CampelloManuel/progetto-esame/datasheets/sonda-ntc_sih010.bmp

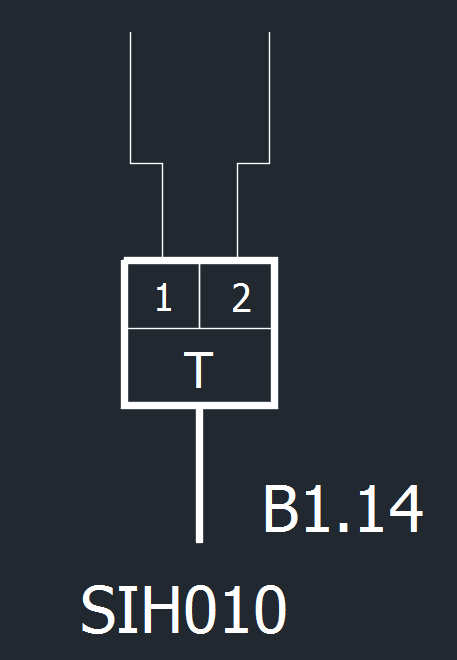
datasheets/sonda-ntc_sih010.bmp
