CampelloManuel/progetto-esame/esempi_arduino/prove_accessori/display_collegamento 2.jpg

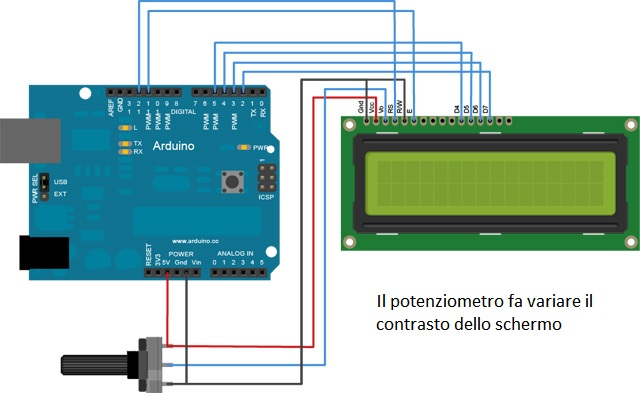
esempi_arduino/prove_accessori/display_collegamento 2.jpg
