CampelloManuel/progetto-esame/immagini_cogeneratore/IMG-20161022-WA0023.jpg

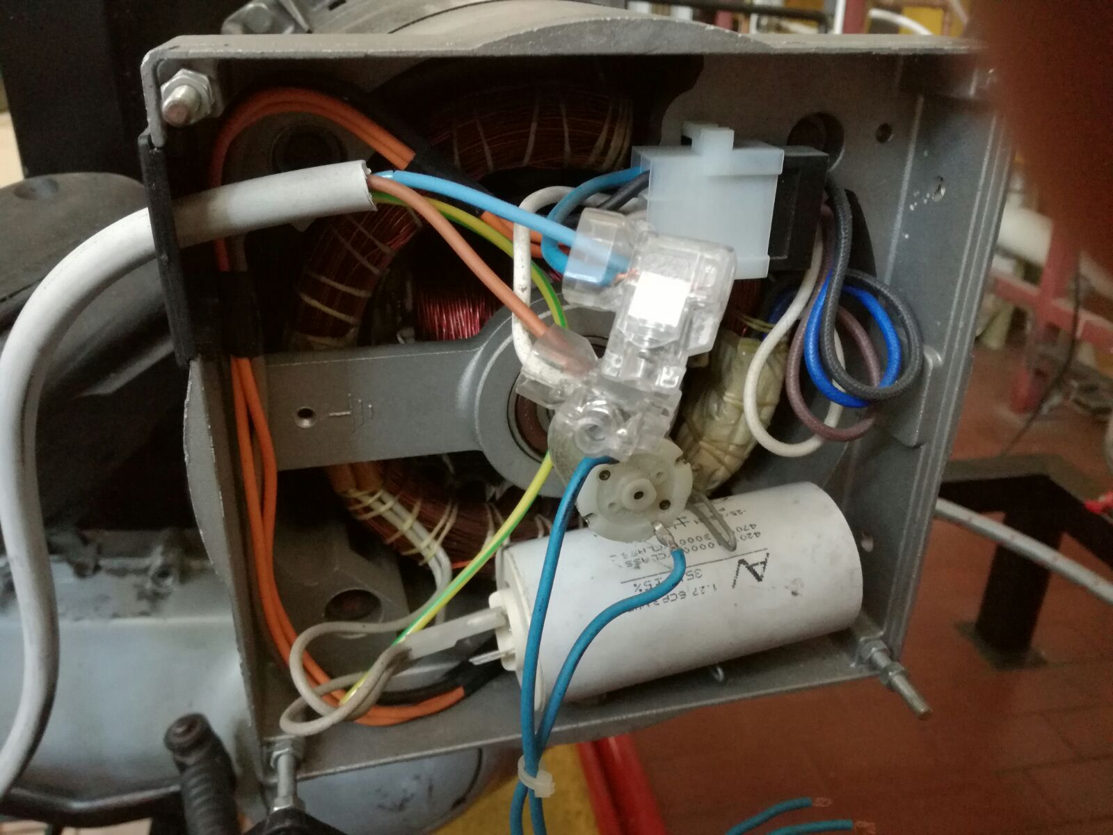
immagini_cogeneratore/IMG-20161022-WA0023.jpg
