CampelloManuel/progetto-esame/immagini_cogeneratore/IMG-20161022-WA0027.jpg

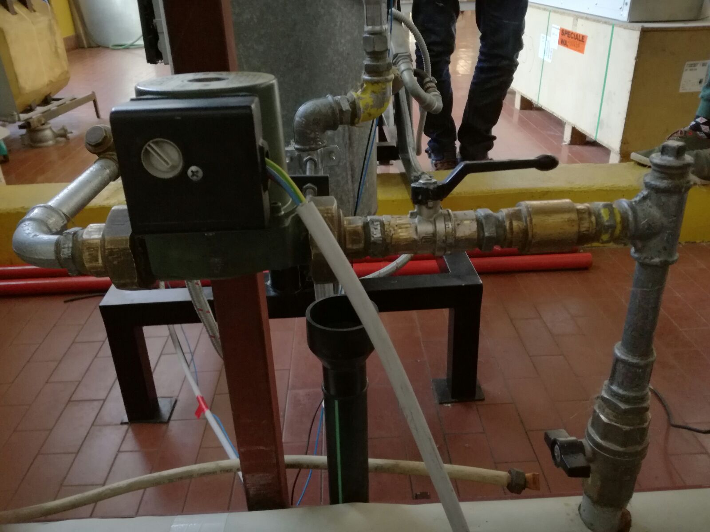
immagini_cogeneratore/IMG-20161022-WA0027.jpg
