CampelloManuel/progetto-esame/immagini_cogeneratore/IMG-20170110-WA0005.jpg

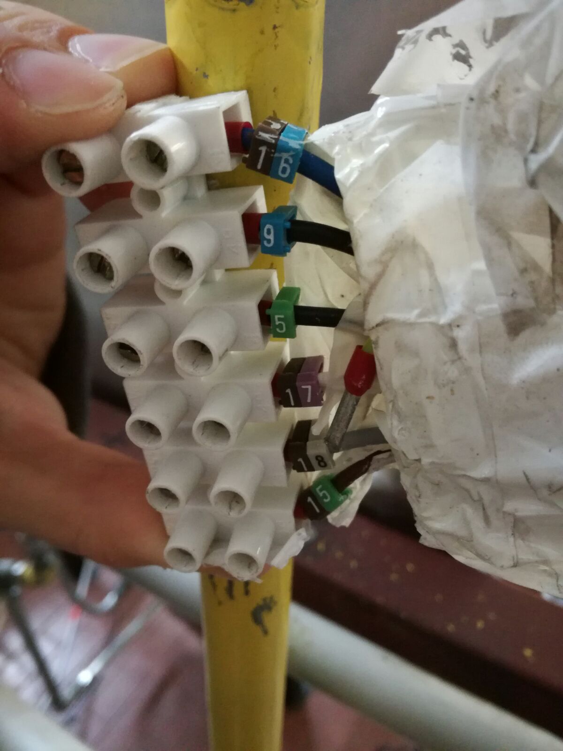
immagini_cogeneratore/IMG-20170110-WA0005.jpg
