CampelloManuel/progetto-esame/immagini_cogeneratore/IMG-20170610-WA0005.jpg

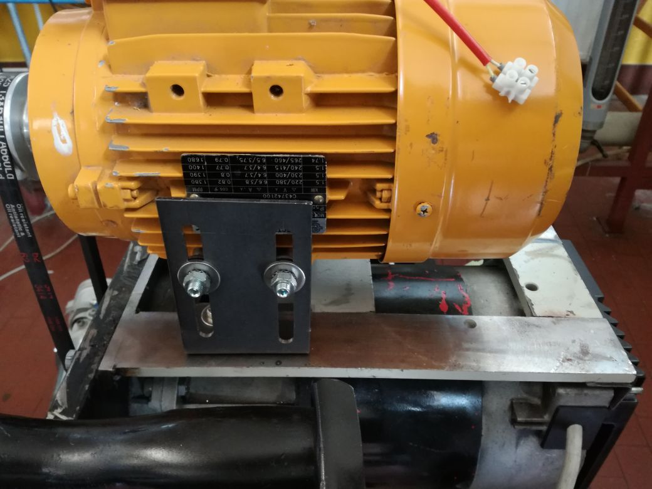
immagini_cogeneratore/IMG-20170610-WA0005.jpg
