CampelloManuel/progetto-esame/immagini_cogeneratore/IMG-20170610-WA0010.jpg

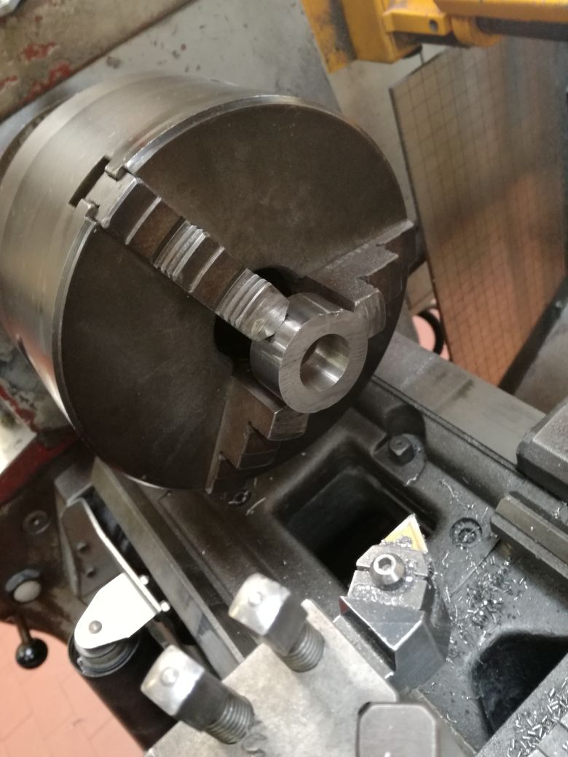
immagini_cogeneratore/IMG-20170610-WA0010.jpg
