CampelloManuel/progetto-esame/immagini_cogeneratore/IMG_20161109_105624.jpg

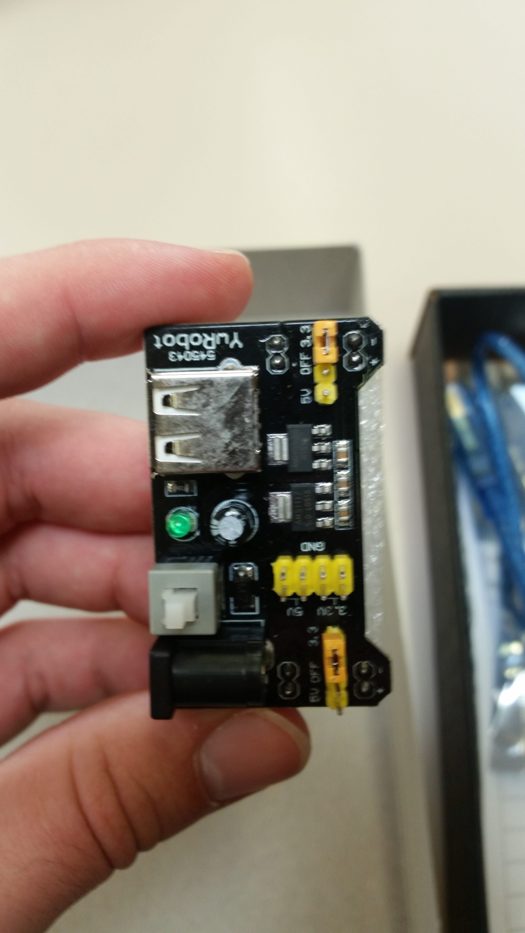
immagini_cogeneratore/IMG_20161109_105624.jpg
