CampelloManuel/progetto-esame/immagini_cogeneratore/IMG_20161201_091057.jpg

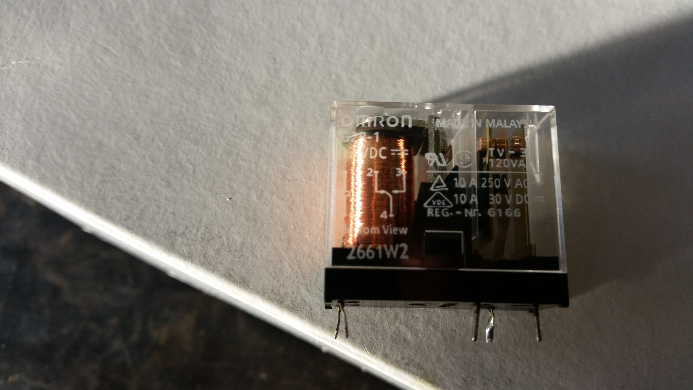
immagini_cogeneratore/IMG_20161201_091057.jpg
