CampelloManuel/progetto-esame/immagini_cogeneratore/IMG_20161201_091629.jpg

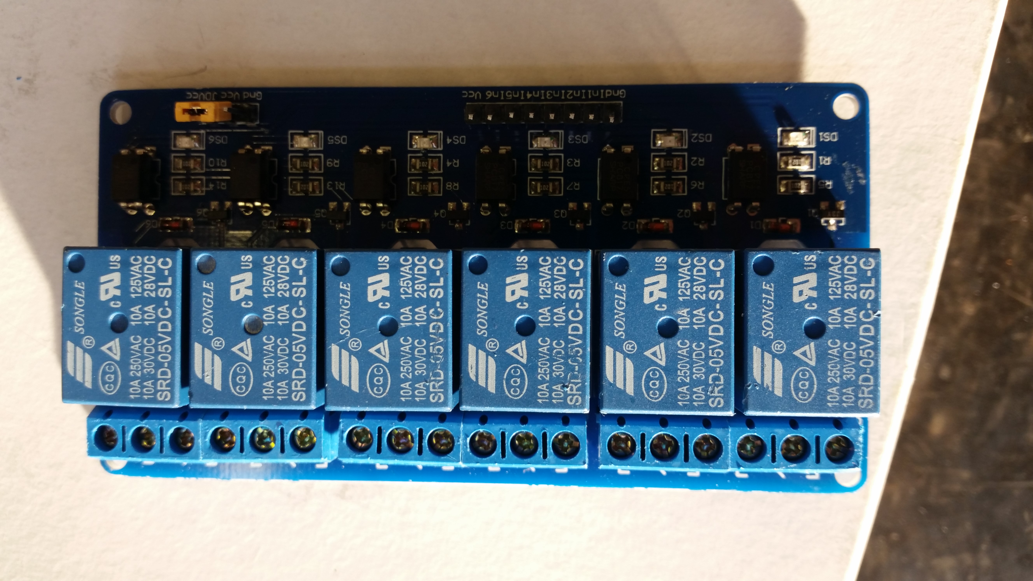
immagini_cogeneratore/IMG_20161201_091629.jpg
