CampelloManuel/progetto-esame/immagini_cogeneratore/IMG_20170113_105047.jpg

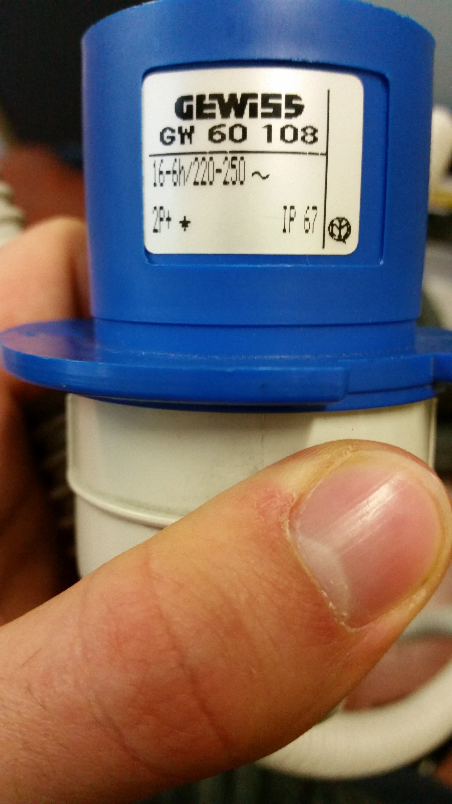
immagini_cogeneratore/IMG_20170113_105047.jpg
