CampelloManuel/progetto-esame/immagini_cogeneratore/IMG_20170113_111320.jpg

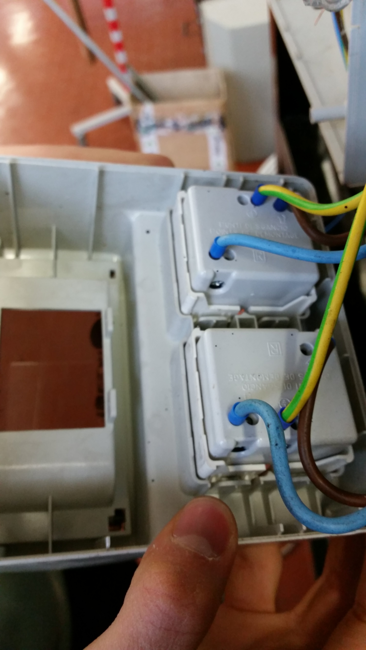
immagini_cogeneratore/IMG_20170113_111320.jpg
