CampelloManuel/progetto-esame/immagini_cogeneratore/IMG_20170120_110058.jpg

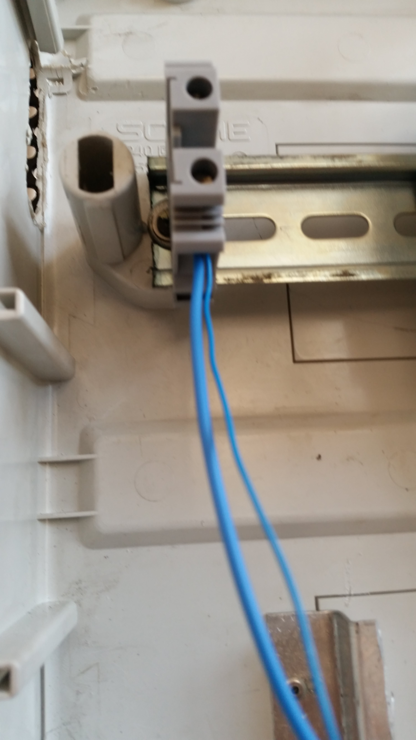
immagini_cogeneratore/IMG_20170120_110058.jpg
