CampelloManuel/progetto-esame/immagini_cogeneratore/IMG_20170120_111345.jpg

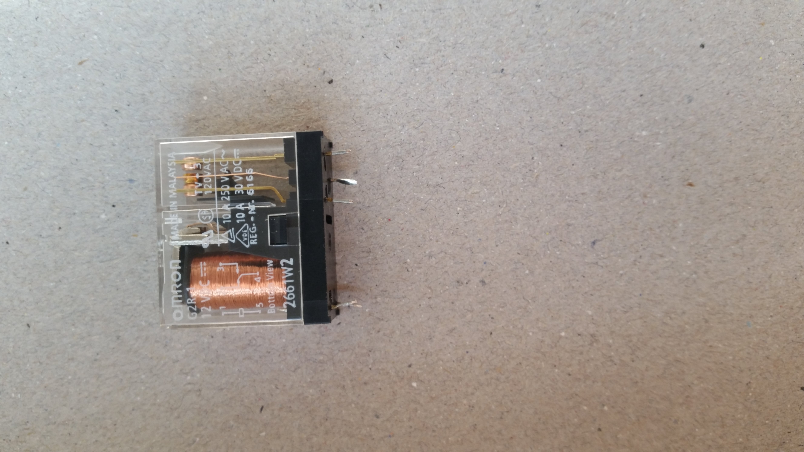
immagini_cogeneratore/IMG_20170120_111345.jpg
