CampelloManuel/progetto-esame/immagini_cogeneratore/IMG_20170317_114829.jpg

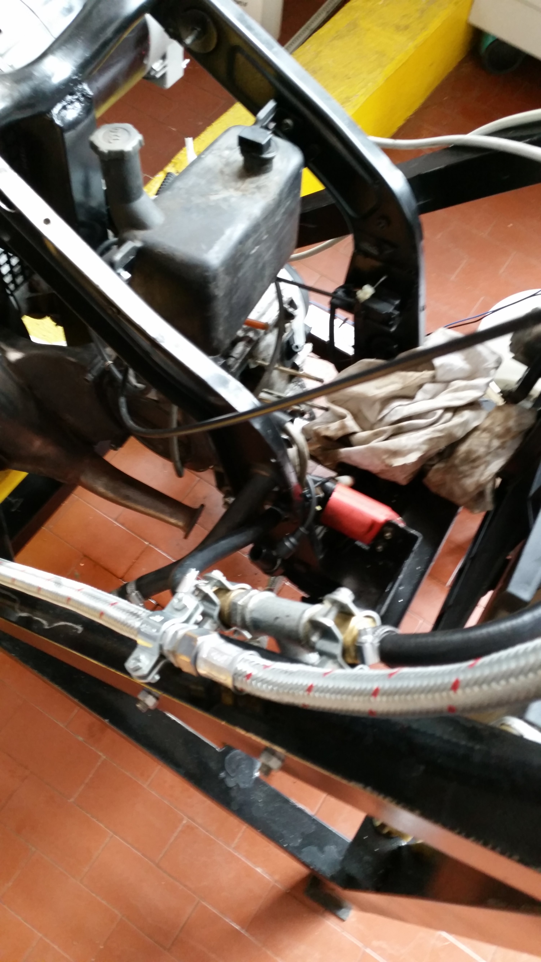
immagini_cogeneratore/IMG_20170317_114829.jpg
