CampelloManuel/progetto-esame/immagini_cogeneratore/IMG_20170317_114911.jpg

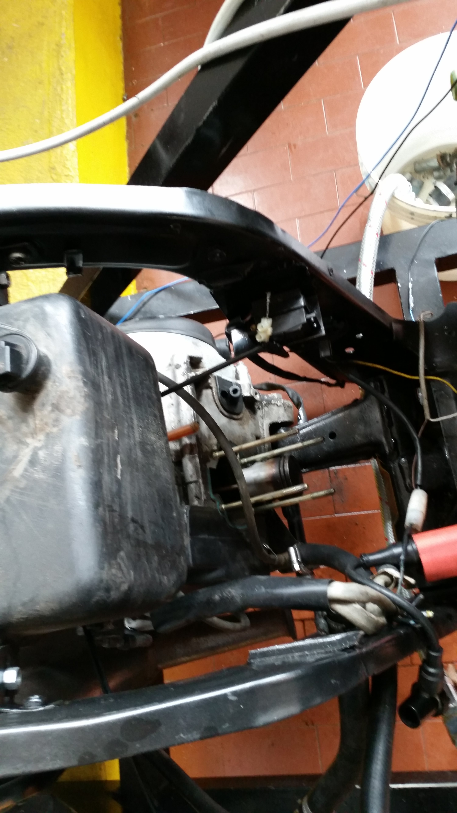
immagini_cogeneratore/IMG_20170317_114911.jpg
