CampelloManuel/progetto-esame/immagini_cogeneratore/IMG_20170317_115021.jpg

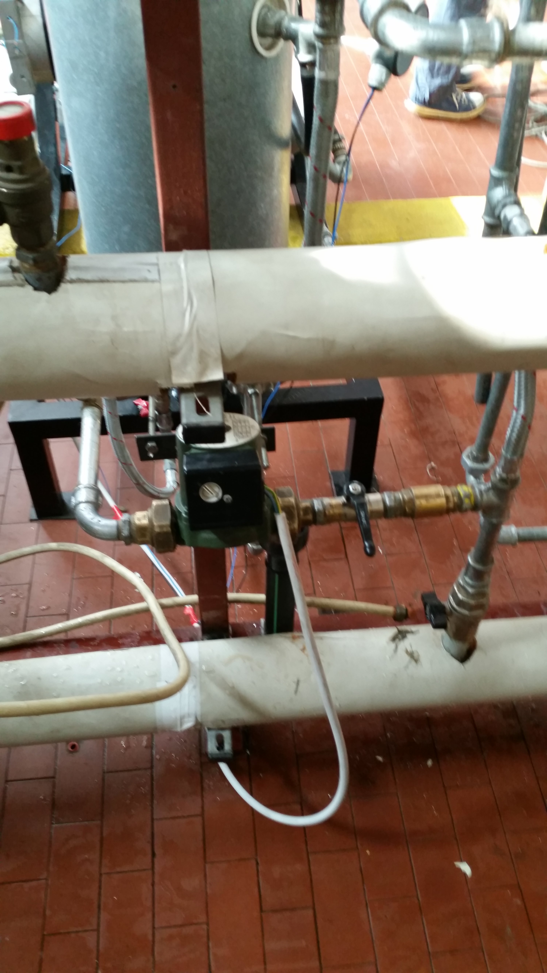
immagini_cogeneratore/IMG_20170317_115021.jpg
