CampelloManuel/progetto-esame/immagini_cogeneratore/IMG_20170503_162917.jpg

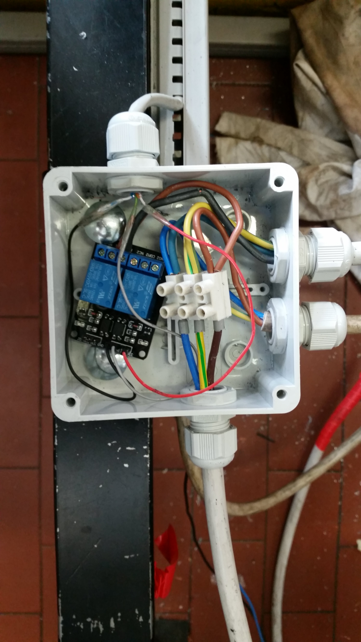
immagini_cogeneratore/IMG_20170503_162917.jpg
