CampelloManuel/progetto-esame/immagini_cogeneratore/IMG_20170527_101132.jpg

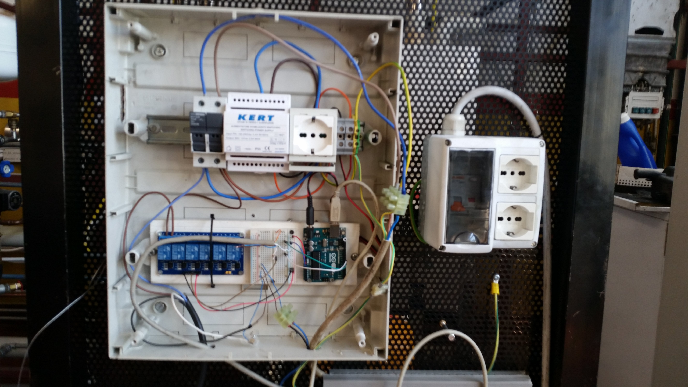
immagini_cogeneratore/IMG_20170527_101132.jpg
