CampelloManuel/progetto-esame/immagini_cogeneratore/IMG_20170527_101155.jpg

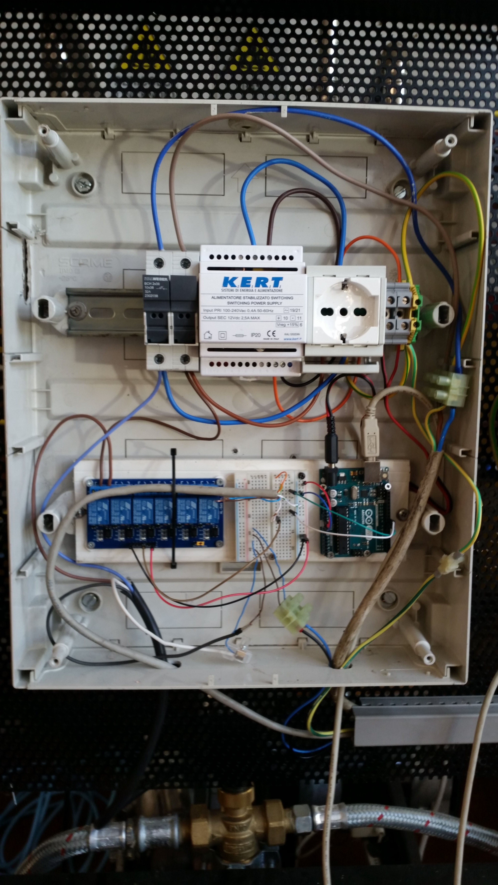
immagini_cogeneratore/IMG_20170527_101155.jpg
