CampelloManuel/progetto-esame/esempi/parti_software_regolazione/bozza_collegamenti/bozza_collegamenti.ino

/* SCHEMA DI COLLEGAMENTO:
 * pin -> funzione
 * -----------------
 * A0 -> "contagiri" motore
 * 2 -> finecorsa valvola a 3 vie
 * 3 -> commutazione relè attivazione valvola a 3 vie (LOW = acceso)
 * 5 -> comando servomotore (per accelerazione motore piaggio)
 * 6 -> segnale a scatola relè di alimentazione
 */

void setup() {
  

}

void loop() {
  

}
