CampelloManuel/progetto-esame/immagini_cogeneratore/IMG_20170110_155340.jpg

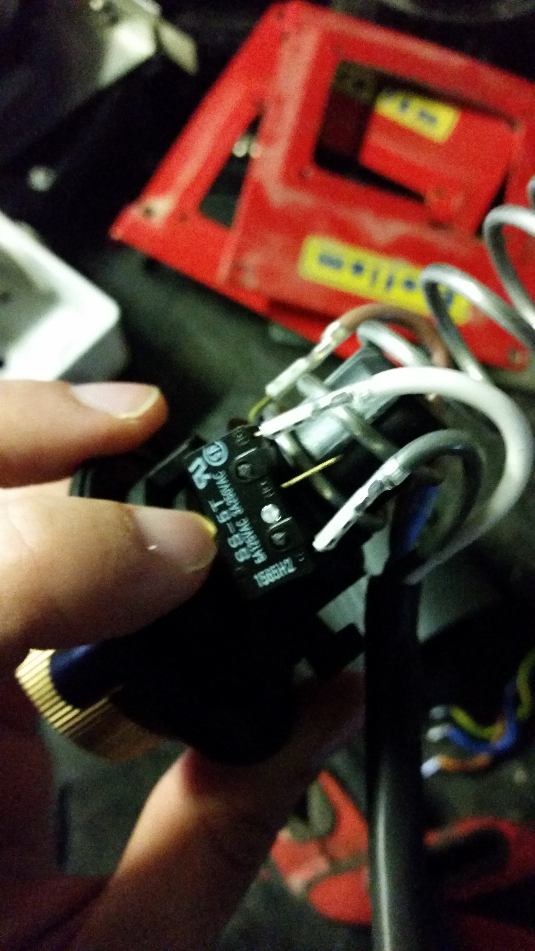
immagini_cogeneratore/IMG_20170110_155340.jpg
