CampelloManuel/progetto-esame/immagini_cogeneratore/IMG_20170316_164335.jpg

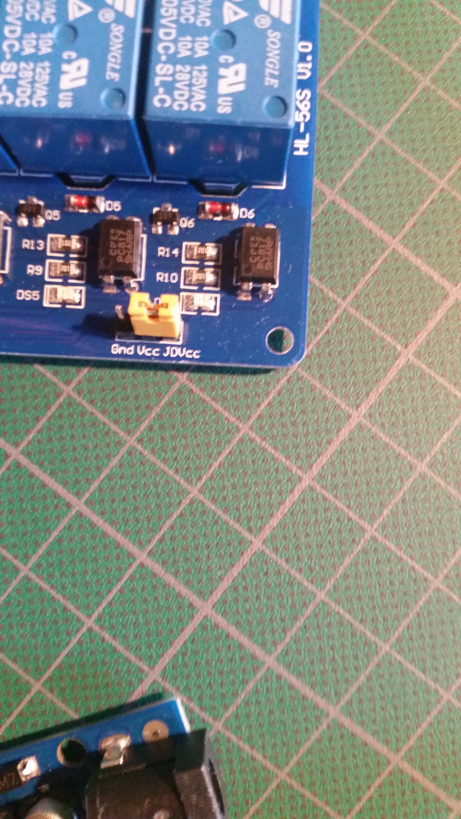
immagini_cogeneratore/IMG_20170316_164335.jpg
